CCHS-Melbourne/iotuz-esp32-hardware/Software/Snippets/fulldemo/Handheld-Color-Console/paddle.cpp

/*
    Arduino Breakout
    Copyright (C) 2015 João André Esteves Vilaça

    https://github.com/vilaca/Handheld-Color-Console

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
    You should have received a copy of the GNU General Public License along
    with this program; if not, write to the Free Software Foundation, Inc.,
    51 Franklin Street, Fifth Floor, Boston, MA 02110-1301 USA.
*/
#ifndef PADDLECPP
#define PADDLECPP

#include "config.h"
#include "iotuz.h" // read_encoder

class Paddle
{
  int x, y;
  
  public:

  // draws paddle on screen when it moves
  // to avoid spending too much time clearing the screen and drawing
  // only the same amount of pixels that the paddle moves are cleared and drawn
  
    void draw(int m)
    {
      // Allow overriding joystick movement with rotary encoder
      static int16_t encoder = 0;
      int16_t new_encoder = read_encoder();
      if (encoder != new_encoder)
      {
	Serial.print("Rot Encoder > ");
	Serial.print(encoder);
	Serial.print(" > ");
	Serial.print(new_encoder);
	m = (encoder-new_encoder) * -2;
	encoder = new_encoder;
	Serial.print(" > ");
	Serial.println(m);
      }
      else
      {
	Serial.print("Joy: ");
	Serial.println(m);
      }
      // ^^^^^
      // Because there are 2 ways to drive the paddle, show on serial console which
      // one is responsible for moving the paddle if it drifts on its own.

      if ( m < 0 && x > PADDLE_W )
      {
        // cant move beyond the screen border
        if ( m < -(x - PADDLE_W)) m = -(x - PADDLE_W);

        // remove part of the old paddle on the left
        tft2.fillRectangle( x + PADDLE_W + m, y, -m, PADDLE_H, BACKGROUND_COLOR);
      
        // add a bit more to the left of the existing paddle
        tft2.fillRectangle( x - PADDLE_W + m, y, -m, PADDLE_H, PADDLE_COLOR);
      
        // remember m < 0
        x+=m;
      }
      else if ( m > 0 && x < MAX_X - PADDLE_W )
      {
        // cant move beyond the screen border
        if ( m > MAX_X - x - PADDLE_W ) m = MAX_X - x - PADDLE_W;
      
        // remove a part of the old paddle on the right
        tft2.fillRectangle( x - PADDLE_W, y, m, PADDLE_H, BACKGROUND_COLOR);
      
        // add a bit more  of paddle to the left of the existing paddle
        tft2.fillRectangle( x + PADDLE_W, y, m, PADDLE_H, PADDLE_COLOR );
      
        x+=m;
      }
    }
  
    // draws paddle the first time
    // all paddle must be drawn
  
    void draw()
    {
      tft2.fillRectangle(x- PADDLE_W, y, PADDLE_W * 2, PADDLE_H, PADDLE_COLOR);
    }
  
    void setXY(int x_, int y_)
    {
      x = x_;
      y = y_;
    }

    int getX()
    {
      return x;
    }

    int getY()
    {
      return y;
    }
};

#endif
