CCHS-Melbourne/iotuz-esp32-hardware/Software/Snippets/fulldemo/Handheld-Color-Console/breakout.cpp

/*
    Arduino Breakout
    Copyright (C) 2015 João André Esteves Vilaça

    https://github.com/vilaca/Handheld-Color-Console

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
    You should have received a copy of the GNU General Public License along
    with this program; if not, write to the Free Software Foundation, Inc.,
    51 Franklin Street, Fifth Floor, Boston, MA 02110-1301 USA.
*/
#ifndef BREAKOUTCPP
#define BREAKOUTCPP

#include "TFTv2_extended.h"
#include "ball.cpp"
#include "paddle.cpp"
#include "joystick.cpp"
#include "config.h"
#include "scoreboard.cpp"
#include "tiles.cpp"

class Breakout
{
  Joystick js;

  Ball ball;
  
  Paddle paddle;

  Scoreboard score;

  Tiles tiles;

  int beep;

  public:
  
    unsigned long last;
  
    Breakout(): ball(BOARD_LEFT, BOARD_RIGHT - BALL_R * 2, BOARD_TOP, MAX_Y - BALL_R){
    }

    void run()
    {

      // blank board

      tft2.fillRectangle(0,            0, MAX_X,             BOARD_TOP,            SCOREBOARD_COLOR);
      tft2.fillRectangle(0,            0, BOARD_LEFT - 1,    MAX_Y - PADDLE_H - 2, SCOREBOARD_COLOR);
      tft2.fillRectangle(BOARD_RIGHT,  0, TILE_W / 2,        MAX_Y - PADDLE_H - 2, SCOREBOARD_COLOR);
      tft2.fillRectangle(BOARD_LEFT, BOARD_TOP, BOARD_RIGHT - BOARD_LEFT , MAX_Y - BOARD_TOP - PADDLE_H, BACKGROUND_COLOR);
      tft2.fillRectangle(0, MAX_Y - PADDLE_H, MAX_X, MAX_Y, BACKGROUND_COLOR);

      score.init();

      // initialize tile matrix
      newLevel();
      paddle.setXY((MAX_X -PADDLE_W)/ 2, MAX_Y - PADDLE_H);
      paddle.draw();

      do
      {
        serve();
        play();

      } while (score.hasLivesLeft());
    
      const char *go ="GAME OVER";
      const int font_size = 5;
      int cursor = (MAX_X - font_size * FONT_SPACE * 9) / 2;

      boolean skip = false;

      for ( int i= 0; i < 9; i++)
      {
        if ( go[i] != ' ')
        {
          tft2.fillRectangle(cursor, 94, FONT_SPACE * font_size - 2, FONT_X * font_size, RED);
          tft2.drawChar(go[i], cursor - FONT_SPACE / 2, 94 + FONT_SPACE / 2, font_size, WHITE);    
        }
      
        cursor += font_size * FONT_SPACE;

        skip = skip || Joystick::fire();

        if ( skip ) continue;

        for (int j = (10-i) * 100; j > 200; j-=1500 / (i+1))
        {
          Beeping::beep(j, 100);
          delay(100);
        }
      }
      while (!Joystick::fire());
    }

  private:

    void serve()
    {
      ball.setXY(paddle.getX(), MAX_Y - PADDLE_H - BALL_R * 2 - 2);
      ball.draw();
      do
      {
        const int m = js.getX();
        if ( m != 0 || encoder_changed())
        {
          paddle.draw(m);
          ball.clear();
          ball.setX(paddle.getX());
          ball.draw();
          delay(5);
        }
      } while (!Joystick::fire());
    }

    void play()
    {
      for(;;)
      {

        unsigned long waited = millis() - last;

        if ( waited > BALL_MOVE_WAIT )
        {
          last = millis();
        
          ball.clear();
          ball.move();
          ball.draw();
        
          if (ball.collision(paddle))
          {
            beep = 200;
            Beeping::beep(400,30);
          }
        
          // check collision w/ tiles
        
          int scored = ball.collision(tiles);

          if ( scored > 0)
          {
            beep *=1.1;
            if ( beep > 3000) beep = 3000;
            Beeping::beep(beep,25);
          }
        
          if (scored > 0)
          {
            score.update(scored);
          
            if ( tiles.allGone() )
            {
              ball.clear();
              newLevel();
              score.nextLevel();
              break;
            }
          }

          if (ball.escaped(paddle))
          {
            score.died();

            for (int i = 54; i > 30; i--)
            {
              Beeping::beep(random(i,i*i), 3);
              delay(6);
            }
          
            ball.clear();
          
            break;
          }
        }

        const int m = js.getX();
	// m is 0 for no movement, negative for left, positive for right
	//Serial.print("Joystick: ");
	//Serial.println(m);
	// ESP32 is too fast and moves the ball too quickly, not giving a chance to move the paddle
	delay(7);
        if (waited > PADDLE_MOVE_WAIT && (m != 0 || encoder_changed()))
        {
  	  //Serial.println("move paddle");
          last = millis();
          paddle.draw(m);
        }
      }
    }

    void newLevel()
    {
      // ANALOG 2 SHOULD NOT BE CONNECTED TO ANYTHING.
      // PLEASE LEAVE PIN FLOATING
    
      randomSeed(analogRead(2));

      tiles.drawAll();

      ball.setXY(MAX_X / 2, MAX_Y - PADDLE_H - BALL_R * 2 - 2);
      ball.setXiYi(-BALL_SPEED_H, -BALL_SPEED_V);
    
      beep = 200;
    }
};

#endif
