CCHS-Melbourne/iotuz-esp32-hardware/Software/Snippets/fulldemo/Handheld-Color-Console/ball.cpp

/*
    Arduino Breakout
    Copyright (C) 2015 João André Esteves Vilaça

    https://github.com/vilaca/Handheld-Color-Console

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
    You should have received a copy of the GNU General Public License along
    with this program; if not, write to the Free Software Foundation, Inc.,
    51 Franklin Street, Fifth Floor, Boston, MA 02110-1301 USA.
*/
#ifndef BALLCPP
#define BALLCPP

#include "tiles.cpp"
#include "config.h"
#include "beeping.cpp"
#include "paddle.cpp"

class Ball
{
  const int SCORE[7] = {0, 1, 1, 3, 5, 5, 7};
  
  int left, right, top, bottom;
  
  float x, y, xi, yi;

  public:
  
    Ball(int left_, int right_, int top_, int bottom_)
    {
      left = left_;
      right = right_;
      top = top_;
      bottom = bottom_;
    }

    void clear()
    {
      tft2.fillRectangle(x, y, BALL_R * 2, BALL_R * 2, BLACK);
    }
  
    void draw()
    {
      tft2.fillRectangle(x, y, BALL_R * 2, BALL_R * 2, BALL_COLOR);
    }

    void setXY(int x_, int y_)
    {
      x = x_;
      y = y_;
    }

    void setX(int x_)
    {
      x = x_;
    }

    void setXiYi(int xi_, int yi_)
    {
      xi = xi_;
      yi = yi_;
    }

    bool escaped(Paddle &paddle)
    {
      return y >= paddle.getY();
    }
  
    void move()
    {
      if((xi < 0 && x + xi < left)||(xi > 0 && x +xi >= right))
      {
        xi *= -1;
      }

      if(yi < 0 && y+yi-BALL_R*2 < top)
      {
        yi *= -1;
      }

      x+= xi;
      y+= yi;
    }

    int getX()
    {
      return x;
    }

    int getY()
    {
      return y;
    }

    int getXi()
    {
      return xi;
    }

    // check for collision with paddle
    // calculate score and bounce

    int collision(Tiles &tiles)
    {
      const int x = this->x+xi;
      const int y = this->y+yi;
    
      int hit;
    
      if ( hit = hitTile( tiles,    x,              y  ))
      {
        return SCORE[hit];
      }
        
      if ( hit = hitTile( tiles,    x + BALL_R * 2, y + BALL_R * 2  ))
      {
        return SCORE[hit];
      }
    
      if ( hit = hitTile( tiles,    x + BALL_R * 2, y  ))
      {
        return SCORE[hit];
      }
    
      hit = hitTile( tiles,         x,              y + BALL_R * 2  );
    
      return SCORE[hit];
    }

    // check for collision with paddle
    // and bounce
    bool collision(Paddle &paddle)
    {
      // only interested if ball is moving down
      if ( yi < 0 ) return false;

      const int ny = y+yi+BALL_R*2;

      if ( ny < paddle.getY() ) return false;
    
      // ball center
      const int bc = x + BALL_R;

      const int diff = bc - paddle.getX();

      if ( diff < -PADDLE_W-PADDLE_TOLERANCE || diff > PADDLE_W + PADDLE_TOLERANCE)
      {
        return false;
      }
      else if (diff > 0)
      {
        const int hit = diff / ((PADDLE_W + PADDLE_TOLERANCE)/2);
        xi = (float)hit * .5f + .5f;
        yi = - 2 + xi;
      }
      else if (diff < 0)
      {
        const int hit = diff / ((PADDLE_W + PADDLE_TOLERANCE)/2);
        xi = (float)hit * .5f - .5f;
        yi = - 2 - xi;
      }
      else
      {
        yi *= -1;
      }
    
      return true;
    }

  private:

    int hitTile(Tiles &tiles, int x, int y)
    {
      int ty =(y - TILES_TOP)/ TILE_H;
      int tx =(x - TILES_LEFT)/ TILE_W;
    
      const boolean hit = ty >= 0 && ty < ROWS && tx >= 0 && tx < COLS && tiles.exists(tx,ty);
    
      if (!hit) return 0;
    
      tiles.clearTile( tx, ty );
    
      const int score = ROWS - ty;
    
      ty*= TILE_H;
      ty+= TILES_TOP;

      tft2.fillRectangle(TILES_LEFT + tx * TILE_W, ty, TILE_W - 2, TILE_H - 2, BACKGROUND_COLOR);
        
      const int ty2= ty + TILE_H;

      if ( (yi > 0 && y > ty) || (yi < 0 && y > ty2))
      {
        xi *=-1;
      }
      else
      {
        yi *=-1;
      }

      return score;
    }
};

#endif
