CCHS-Melbourne/iotuz-esp32-hardware/Software/Snippets/fulldemo/adafruit_breakouttouchpaint.ino

/***************************************************
  This is our touchscreen painting example for the Adafruit ILI9341 Breakout
  ----> http://www.adafruit.com/products/1770

  Check out the links above for our tutorials and wiring diagrams
  These displays use SPI to communicate, 4 or 5 pins are required to
  interface (RST is optional)
  Adafruit invests time and resources providing this open source code,
  please support Adafruit and open-source hardware by purchasing
  products from Adafruit!

  Written by Limor Fried/Ladyada for Adafruit Industries.
  MIT license, all text above must be included in any redistribution
 ****************************************************/

/** NOT FOR USE WITH THE TOUCH SHIELD, ONLY FOR THE BREAKOUT! **/

// Size of the color selection boxes and the paintbrush size
#define BOXSIZE 40
#define PENRADIUS 2
int oldcolor, currentcolor;

void touchpaint_setup(void) {
  // make the color selection boxes
  tft.fillRect(0, 0,         BOXSIZE, BOXSIZE, ILI9341_RED);
  tft.fillRect(BOXSIZE, 0,   BOXSIZE, BOXSIZE, ILI9341_YELLOW);
  tft.fillRect(BOXSIZE*2, 0, BOXSIZE, BOXSIZE, ILI9341_GREEN);
  tft.fillRect(BOXSIZE*3, 0, BOXSIZE, BOXSIZE, ILI9341_CYAN);
  tft.fillRect(BOXSIZE*4, 0, BOXSIZE, BOXSIZE, ILI9341_BLUE);
  tft.fillRect(BOXSIZE*5, 0, BOXSIZE, BOXSIZE, ILI9341_MAGENTA);
  // offset 6 is 'black'
  tft.fillRect(BOXSIZE*7, 0, BOXSIZE, BOXSIZE, ILI9341_WHITE);
 
  // select the current color 'red'
  tft.drawRect(0, 0, BOXSIZE, BOXSIZE, ILI9341_WHITE);
  currentcolor = ILI9341_RED;
}


void touchpaint_loop()
{
  // Retrieve a point  
  i2cexp_clear_bits(I2CEXP_TOUCH_CS);

  TS_Point p = ts.getPoint();
  i2cexp_set_bits(I2CEXP_TOUCH_CS);

  
  Serial.print("X = "); Serial.print(p.x);
  Serial.print("\tY = "); Serial.print(p.y);
  Serial.print("\tPressure = "); Serial.println(p.z);  
  
  // we have some minimum pressure we consider 'valid'
  // pressure of 0 means no pressing!
  if (p.z < MINPRESSURE || p.z > MAXPRESSURE) {
     return;
  }
  
  // Scale from ~0->1000 to tft.width using the calibration #'s
  p.x = map(p.x, TS_MINX, TS_MAXX, 0, tft.width());
  p.y = map(p.y, TS_MINY, TS_MAXY, 0, tft.height());

  Serial.print("("); Serial.print(p.x);
  Serial.print(", "); Serial.print(p.y);
  Serial.println(")");

    
  if (p.y < BOXSIZE) {
     oldcolor = currentcolor;

     if (p.x < BOXSIZE) { 
       currentcolor = ILI9341_RED; 
       tft.drawRect(0, 0, BOXSIZE, BOXSIZE, ILI9341_WHITE);
     } else if (p.x < BOXSIZE*2) {
       currentcolor = ILI9341_YELLOW;
       tft.drawRect(BOXSIZE, 0, BOXSIZE, BOXSIZE, ILI9341_WHITE);
     } else if (p.x < BOXSIZE*3) {
       currentcolor = ILI9341_GREEN;
       tft.drawRect(BOXSIZE*2, 0, BOXSIZE, BOXSIZE, ILI9341_WHITE);
     } else if (p.x < BOXSIZE*4) {
       currentcolor = ILI9341_CYAN;
       tft.drawRect(BOXSIZE*3, 0, BOXSIZE, BOXSIZE, ILI9341_WHITE);
     } else if (p.x < BOXSIZE*5) {
       currentcolor = ILI9341_BLUE;
       tft.drawRect(BOXSIZE*4, 0, BOXSIZE, BOXSIZE, ILI9341_WHITE);
     } else if (p.x < BOXSIZE*6) {
       currentcolor = ILI9341_MAGENTA;
       tft.drawRect(BOXSIZE*5, 0, BOXSIZE, BOXSIZE, ILI9341_WHITE);
     } else if (p.x < BOXSIZE*7) {
       currentcolor = ILI9341_BLACK;
       tft.drawRect(BOXSIZE*6, 0, BOXSIZE, BOXSIZE, ILI9341_WHITE);
     } else if (p.x < BOXSIZE*8) {
       currentcolor = ILI9341_WHITE;
       tft.drawRect(BOXSIZE*7, 0, BOXSIZE, BOXSIZE, ILI9341_BLUE);
     }

     if (oldcolor != currentcolor) {
        if (oldcolor == ILI9341_RED) 
          tft.fillRect(0, 0, BOXSIZE, BOXSIZE, ILI9341_RED);
        if (oldcolor == ILI9341_YELLOW) 
          tft.fillRect(BOXSIZE, 0, BOXSIZE, BOXSIZE, ILI9341_YELLOW);
        if (oldcolor == ILI9341_GREEN) 
          tft.fillRect(BOXSIZE*2, 0, BOXSIZE, BOXSIZE, ILI9341_GREEN);
        if (oldcolor == ILI9341_CYAN) 
          tft.fillRect(BOXSIZE*3, 0, BOXSIZE, BOXSIZE, ILI9341_CYAN);
        if (oldcolor == ILI9341_BLUE) 
          tft.fillRect(BOXSIZE*4, 0, BOXSIZE, BOXSIZE, ILI9341_BLUE);
        if (oldcolor == ILI9341_MAGENTA) 
          tft.fillRect(BOXSIZE*5, 0, BOXSIZE, BOXSIZE, ILI9341_MAGENTA);
        if (oldcolor == ILI9341_BLACK) 
          tft.fillRect(BOXSIZE*6, 0, BOXSIZE, BOXSIZE, ILI9341_BLACK);
        if (oldcolor == ILI9341_WHITE) 
          tft.fillRect(BOXSIZE*7, 0, BOXSIZE, BOXSIZE, ILI9341_WHITE);
     }
  }
  if (((p.y-PENRADIUS) > BOXSIZE) && ((p.y+PENRADIUS) < tft.height())) {
    tft.fillCircle(p.x, p.y, PENRADIUS, currentcolor);
  }
}
