CCHS-Melbourne/iotuz-esp32-hardware/Software/Snippets/fulldemo/Handheld-Color-Console/joystick.cpp

/*
    Arduino Tetris
    Copyright (C) 2015 João André Esteves Vilaça 
    
    https://github.com/vilaca/Handheld-Color-Console

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
    You should have received a copy of the GNU General Public License along
    with this program; if not, write to the Free Software Foundation, Inc.,
    51 Franklin Street, Fifth Floor, Boston, MA 02110-1301 USA.
*/
#ifndef JOYSTICKCPP
#define JOYSTICKCPP

#include <Arduino.h>
#include "iotuz.h"

class Joystick
{
  public:

    // joystick position constants 
    
    static const int NEUTRAL = 0;
    static const int SOFT = 1;
    static const int HARD = 2;
    static const int HARDER = 3;

    static void init ()
    {
      pinMode ( JOYSTICK_BUT_PIN, INPUT_PULLUP );
    }

    static int getX()
    {
      return getPosition(JOYSTICK_X_PIN) * -1;
    }

    static int getY()
    {
      return getPosition(JOYSTICK_Y_PIN);
    }

    static boolean fire()
    {
      return (digitalRead(JOYSTICK_BUT_PIN) == LOW || read_encoder_button() == ENC_DOWN);
    }

    static void waitForRelease()
    {
      while (fire());
    }

    static void waitForRelease(int howLong)
    {
      int c = 0;
      do
      {
        delay (10);
        c += 10;
      }
      while ((fire() || getY() != 0 || getX() != 0) && c < howLong);
    }

    static void waitForClick()
    {
      while (!fire());
    }

  private:

    static int getPosition (int pin)
    {
      int n = analogRead(pin);
      int newn;

      //Serial.print("pin ");
      //Serial.print(pin);
      //Serial.print(": ");
      //Serial.print(n);
    
      // allow for a huge dead zone in the middle ot compensate for bad joysticks
      // that are different between boards
      // First, map the bottom part of the range.
      newn = map(n, 0, 1600, -5, 0);
      // then if we're higher than that, clip the middle and start counting any movement
      // past 2300.
      if (n > 1600) newn = map(constrain(n, 2400, 4095), 2400, 4095, 0, 5);
      // this should yield a result between -5 and +5 that skips the center.
      //Serial.print(" > ");
      //Serial.println(newn);
    
      // Analog 0-4096 is turned into 1>5 for a speed to the left, -1>-5 for a speed to the right
      return newn;
    }
};

#endif
